staskevich/MIDIWidget/Firmware/Descriptors.c

/*
             LUFA Library
     Copyright (C) Dean Camera, 2014.

  dean [at] fourwalledcubicle [dot] com
           www.lufa-lib.org
*/

/*
 * MIDIWidget
 * www.midiwidget.com
 * copyright John Staskevich, 2015
 * john@codeandcopper.com
 *
 * This work is licensed under a Creative Commons Attribution 4.0 International License.
 * http://creativecommons.org/licenses/by/4.0/
 *
 */

/** \file
 *
 *  USB Device Descriptors, for library use when in USB device mode. Descriptors are special
 *  computer-readable structures which the host requests upon device enumeration, to determine
 *  the device's capabilities and functions.
 */

#include "Descriptors.h"

/** Device descriptor structure. This descriptor, located in FLASH memory, describes the overall
 *  device characteristics, including the supported USB version, control endpoint size and the
 *  number of device configurations. The descriptor is read out by the USB host when the enumeration
 *  process begins.
 */
const USB_Descriptor_Device_t PROGMEM DeviceDescriptor =
{
	.Header                 = {.Size = sizeof(USB_Descriptor_Device_t), .Type = DTYPE_Device},

	.USBSpecification       = VERSION_BCD(1,1,0),
	.Class                  = USB_CSCP_NoDeviceClass,
	.SubClass               = USB_CSCP_NoDeviceSubclass,
	.Protocol               = USB_CSCP_NoDeviceProtocol,

	.Endpoint0Size          = FIXED_CONTROL_ENDPOINT_SIZE,

	.VendorID               = 0xFFFF,
	.ProductID              = 0x2048,
	.ReleaseNumber          = VERSION_BCD(0,0,1),

	.ManufacturerStrIndex   = STRING_ID_Manufacturer,
	.ProductStrIndex        = STRING_ID_Product,
	.SerialNumStrIndex      = NO_DESCRIPTOR,

	.NumberOfConfigurations = FIXED_NUM_CONFIGURATIONS
};

/** Configuration descriptor structure. This descriptor, located in FLASH memory, describes the usage
 *  of the device in one of its supported configurations, including information about any device interfaces
 *  and endpoints. The descriptor is read out by the USB host during the enumeration process when selecting
 *  a configuration so that the host may correctly communicate with the USB device.
 */
const USB_Descriptor_Configuration_t PROGMEM ConfigurationDescriptor =
{
	.Config =
		{
			.Header                   = {.Size = sizeof(USB_Descriptor_Configuration_Header_t), .Type = DTYPE_Configuration},

			.TotalConfigurationSize   = sizeof(USB_Descriptor_Configuration_t),
			.TotalInterfaces          = 2,

			.ConfigurationNumber      = 1,
			.ConfigurationStrIndex    = NO_DESCRIPTOR,

			.ConfigAttributes         = (USB_CONFIG_ATTR_RESERVED | USB_CONFIG_ATTR_SELFPOWERED),

			.MaxPowerConsumption      = USB_CONFIG_POWER_MA(100)
		},

	.Audio_ControlInterface =
		{
			.Header                   = {.Size = sizeof(USB_Descriptor_Interface_t), .Type = DTYPE_Interface},

			.InterfaceNumber          = INTERFACE_ID_AudioControl,
			.AlternateSetting         = 0,

			.TotalEndpoints           = 0,

			.Class                    = AUDIO_CSCP_AudioClass,
			.SubClass                 = AUDIO_CSCP_ControlSubclass,
			.Protocol                 = AUDIO_CSCP_ControlProtocol,

			.InterfaceStrIndex        = NO_DESCRIPTOR
		},

	.Audio_ControlInterface_SPC =
		{
			.Header                   = {.Size = sizeof(USB_Audio_Descriptor_Interface_AC_t), .Type = DTYPE_CSInterface},
			.Subtype                  = AUDIO_DSUBTYPE_CSInterface_Header,

			.ACSpecification          = VERSION_BCD(1,0,0),
			.TotalLength              = sizeof(USB_Audio_Descriptor_Interface_AC_t),

			.InCollection             = 1,
			.InterfaceNumber          = INTERFACE_ID_AudioStream,
		},

	.Audio_StreamInterface =
		{
			.Header                   = {.Size = sizeof(USB_Descriptor_Interface_t), .Type = DTYPE_Interface},

			.InterfaceNumber          = INTERFACE_ID_AudioStream,
			.AlternateSetting         = 0,

			.TotalEndpoints           = 2,

			.Class                    = AUDIO_CSCP_AudioClass,
			.SubClass                 = AUDIO_CSCP_MIDIStreamingSubclass,
			.Protocol                 = AUDIO_CSCP_StreamingProtocol,

			.InterfaceStrIndex        = NO_DESCRIPTOR
		},

	.Audio_StreamInterface_SPC =
		{
			.Header                   = {.Size = sizeof(USB_MIDI_Descriptor_AudioInterface_AS_t), .Type = DTYPE_CSInterface},
			.Subtype                  = AUDIO_DSUBTYPE_CSInterface_General,

			.AudioSpecification       = VERSION_BCD(1,0,0),

			.TotalLength              = (sizeof(USB_Descriptor_Configuration_t) -
			                             offsetof(USB_Descriptor_Configuration_t, Audio_StreamInterface_SPC))
		},

	.MIDI_In_Jack_Emb =
		{
			.Header                   = {.Size = sizeof(USB_MIDI_Descriptor_InputJack_t), .Type = DTYPE_CSInterface},
			.Subtype                  = AUDIO_DSUBTYPE_CSInterface_InputTerminal,

			.JackType                 = MIDI_JACKTYPE_Embedded,
			.JackID                   = 0x01,

			.JackStrIndex             = NO_DESCRIPTOR
		},

	.MIDI_In_Jack_Ext =
		{
			.Header                   = {.Size = sizeof(USB_MIDI_Descriptor_InputJack_t), .Type = DTYPE_CSInterface},
			.Subtype                  = AUDIO_DSUBTYPE_CSInterface_InputTerminal,

			.JackType                 = MIDI_JACKTYPE_External,
			.JackID                   = 0x02,

			.JackStrIndex             = NO_DESCRIPTOR
		},

	.MIDI_Out_Jack_Emb =
		{
			.Header                   = {.Size = sizeof(USB_MIDI_Descriptor_OutputJack_t), .Type = DTYPE_CSInterface},
			.Subtype                  = AUDIO_DSUBTYPE_CSInterface_OutputTerminal,

			.JackType                 = MIDI_JACKTYPE_Embedded,
			.JackID                   = 0x03,

			.NumberOfPins             = 1,
			.SourceJackID             = {0x02},
			.SourcePinID              = {0x01},

			.JackStrIndex             = NO_DESCRIPTOR
		},

	.MIDI_Out_Jack_Ext =
		{
			.Header                   = {.Size = sizeof(USB_MIDI_Descriptor_OutputJack_t), .Type = DTYPE_CSInterface},
			.Subtype                  = AUDIO_DSUBTYPE_CSInterface_OutputTerminal,

			.JackType                 = MIDI_JACKTYPE_External,
			.JackID                   = 0x04,

			.NumberOfPins             = 1,
			.SourceJackID             = {0x01},
			.SourcePinID              = {0x01},

			.JackStrIndex             = NO_DESCRIPTOR
		},

	.MIDI_In_Jack_Endpoint =
		{
			.Endpoint =
				{
					.Header              = {.Size = sizeof(USB_Audio_Descriptor_StreamEndpoint_Std_t), .Type = DTYPE_Endpoint},

					.EndpointAddress     = MIDI_STREAM_OUT_EPADDR,
					.Attributes          = (EP_TYPE_BULK | ENDPOINT_ATTR_NO_SYNC | ENDPOINT_USAGE_DATA),
					.EndpointSize        = MIDI_STREAM_EPSIZE,
					.PollingIntervalMS   = 0x05
				},

			.Refresh                  = 0,
			.SyncEndpointNumber       = 0
		},

	.MIDI_In_Jack_Endpoint_SPC =
		{
			.Header                   = {.Size = sizeof(USB_MIDI_Descriptor_Jack_Endpoint_t), .Type = DTYPE_CSEndpoint},
			.Subtype                  = AUDIO_DSUBTYPE_CSEndpoint_General,

			.TotalEmbeddedJacks       = 0x01,
			.AssociatedJackID         = {0x01}
		},

	.MIDI_Out_Jack_Endpoint =
		{
			.Endpoint =
				{
					.Header              = {.Size = sizeof(USB_Audio_Descriptor_StreamEndpoint_Std_t), .Type = DTYPE_Endpoint},

					.EndpointAddress     = MIDI_STREAM_IN_EPADDR,
					.Attributes          = (EP_TYPE_BULK | ENDPOINT_ATTR_NO_SYNC | ENDPOINT_USAGE_DATA),
					.EndpointSize        = MIDI_STREAM_EPSIZE,
					.PollingIntervalMS   = 0x05
				},

			.Refresh                  = 0,
			.SyncEndpointNumber       = 0
		},

	.MIDI_Out_Jack_Endpoint_SPC =
		{
			.Header                   = {.Size = sizeof(USB_MIDI_Descriptor_Jack_Endpoint_t), .Type = DTYPE_CSEndpoint},
			.Subtype                  = AUDIO_DSUBTYPE_CSEndpoint_General,

			.TotalEmbeddedJacks       = 0x01,
			.AssociatedJackID         = {0x03}
		}
};

/** Language descriptor structure. This descriptor, located in FLASH memory, is returned when the host requests
 *  the string descriptor with index 0 (the first index). It is actually an array of 16-bit integers, which indicate
 *  via the language ID table available at USB.org what languages the device supports for its string descriptors.
 */
const USB_Descriptor_String_t PROGMEM LanguageString = USB_STRING_DESCRIPTOR_ARRAY(LANGUAGE_ID_ENG);

/** Manufacturer descriptor string. This is a Unicode string containing the manufacturer's details in human readable
 *  form, and is read out upon request by the host when the appropriate string ID is requested, listed in the Device
 *  Descriptor.
 */
const USB_Descriptor_String_t PROGMEM ManufacturerString = USB_STRING_DESCRIPTOR(L"Code and Copper LLC");

/** Product descriptor string. This is a Unicode string containing the product's details in human readable form,
 *  and is read out upon request by the host when the appropriate string ID is requested, listed in the Device
 *  Descriptor.
 */
const USB_Descriptor_String_t PROGMEM ProductString = USB_STRING_DESCRIPTOR(L"MIDIWidget");

/** This function is called by the library when in device mode, and must be overridden (see library "USB Descriptors"
 *  documentation) by the application code so that the address and size of a requested descriptor can be given
 *  to the USB library. When the device receives a Get Descriptor request on the control endpoint, this function
 *  is called so that the descriptor details can be passed back and the appropriate descriptor sent back to the
 *  USB host.
 */
uint16_t CALLBACK_USB_GetDescriptor(const uint16_t wValue,
                                    const uint8_t wIndex,
                                    const void** const DescriptorAddress)
{
	const uint8_t  DescriptorType   = (wValue >> 8);
	const uint8_t  DescriptorNumber = (wValue & 0xFF);

	const void* Address = NULL;
	uint16_t    Size    = NO_DESCRIPTOR;

	switch (DescriptorType)
	{
		case DTYPE_Device:
			Address = &DeviceDescriptor;
			Size    = sizeof(USB_Descriptor_Device_t);
			break;
		case DTYPE_Configuration:
			Address = &ConfigurationDescriptor;
			Size    = sizeof(USB_Descriptor_Configuration_t);
			break;
		case DTYPE_String:
			switch (DescriptorNumber)
			{
				case STRING_ID_Language:
					Address = &LanguageString;
					Size    = pgm_read_byte(&LanguageString.Header.Size);
					break;
				case STRING_ID_Manufacturer:
					Address = &ManufacturerString;
					Size    = pgm_read_byte(&ManufacturerString.Header.Size);
					break;
				case STRING_ID_Product:
					Address = &ProductString;
					Size    = pgm_read_byte(&ProductString.Header.Size);
					break;
			}

			break;
	}

	*DescriptorAddress = Address;
	return Size;
}
