staskevich/MIDIWidget/Firmware/EEData.c

/*
 * MIDIWidget
 * www.midiwidget.com
 * copyright John Staskevich, 2015
 * john@codeandcopper.com
 *
 * This work is licensed under a Creative Commons Attribution 4.0 International License.
 * http://creativecommons.org/licenses/by/4.0/
 *
 * Eedata.c
 *
 * Variables located in non-volatile data memory.
 */ 

#include "MIDIWidget.h"

uint8_t OUTPUT_CONFIG[NUM_OUTPUTS * CONFIG_CHUNK_SIZE] EEMEM =
{
	// mode, channel, number, threshold, duration_h, duration_l, reserved, inverted
	OUTPUT_MODE_NOTE, 0x00, 0x3C, 0x01, 0x00, 0x00, 0x00, 0x00, 0x00, 0x00, 0x00, 0x00, 0x00, 0x00, 0x00, 0x00,
	OUTPUT_MODE_NOTE, 0x00, 0x3D, 0x01, 0x00, 0x00, 0x00, 0x00, 0x00, 0x00, 0x00, 0x00, 0x00, 0x00, 0x00, 0x00,
	OUTPUT_MODE_NOTE, 0x00, 0x3E, 0x01, 0x00, 0x00, 0x00, 0x00, 0x00, 0x00, 0x00, 0x00, 0x00, 0x00, 0x00, 0x00,
	OUTPUT_MODE_NOTE, 0x00, 0x3F, 0x01, 0x00, 0x00, 0x00, 0x00, 0x00, 0x00, 0x00, 0x00, 0x00, 0x00, 0x00, 0x00,
	OUTPUT_MODE_NOTE, 0x00, 0x40, 0x01, 0x00, 0x00, 0x00, 0x00, 0x00, 0x00, 0x00, 0x00, 0x00, 0x00, 0x00, 0x00,
	OUTPUT_MODE_NOTE, 0x00, 0x41, 0x01, 0x00, 0x00, 0x00, 0x00, 0x00, 0x00, 0x00, 0x00, 0x00, 0x00, 0x00, 0x00,
	OUTPUT_MODE_NOTE, 0x00, 0x42, 0x01, 0x00, 0x00, 0x00, 0x00, 0x00, 0x00, 0x00, 0x00, 0x00, 0x00, 0x00, 0x00,
	OUTPUT_MODE_NOTE, 0x00, 0x43, 0x01, 0x00, 0x00, 0x00, 0x00, 0x00, 0x00, 0x00, 0x00, 0x00, 0x00, 0x00, 0x00,

	OUTPUT_MODE_NOTE, 0x00, 0x44, 0x01, 0x00, 0x00, 0x00, 0x00, 0x00, 0x00, 0x00, 0x00, 0x00, 0x00, 0x00, 0x00,
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
uint8_t CONFIG_PRESET_RECALL_CHANNEL EEMEM = 0x00;
uint8_t CONFIG_PRESET_RECALL_TYPE EEMEM = MESSAGE_TYPE_NONE;

uint8_t CONFIG_OPERATION_FLAGS EEMEM = 0b00000000;

uint8_t FIRMWARE_VERSION EEMEM = 0x00;
uint8_t ReservedEEPROMByte0 EEMEM = 0x00;
